sparkfun/SparkFun_Qwiic_5V_Boost_AP3012K/docs/assets/img/feature.png

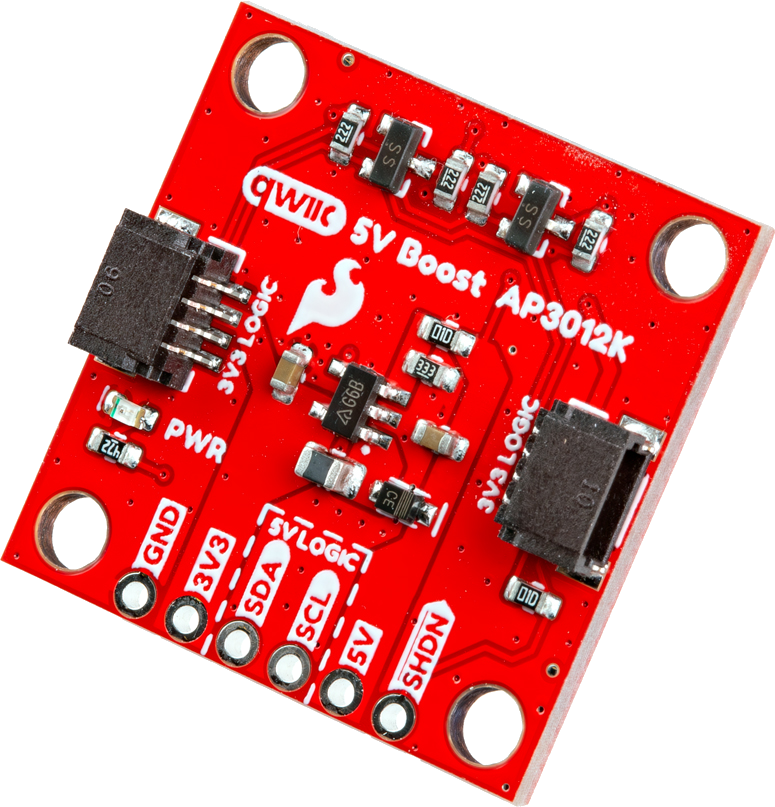
docs/assets/img/feature.png
